indigo255/stm32businesscard/writeup/DS1Z_QuickPrint1.png

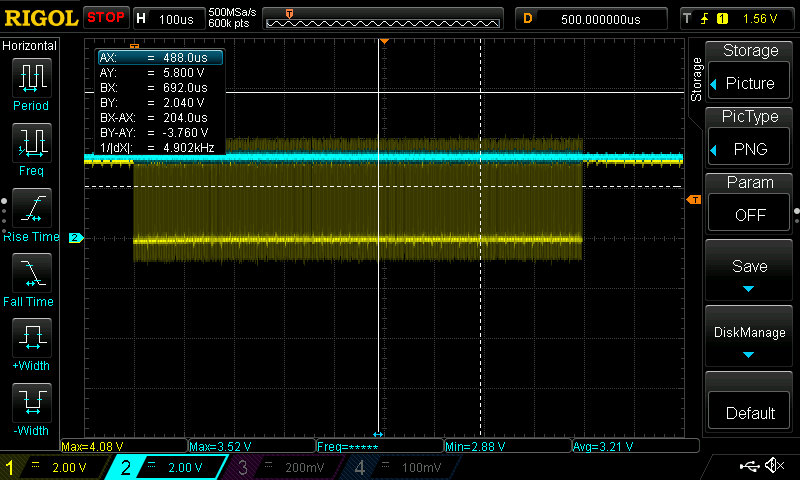
writeup/DS1Z_QuickPrint1.png
